Strooom/SmartTherm/docs/Blynk Interface.PNG

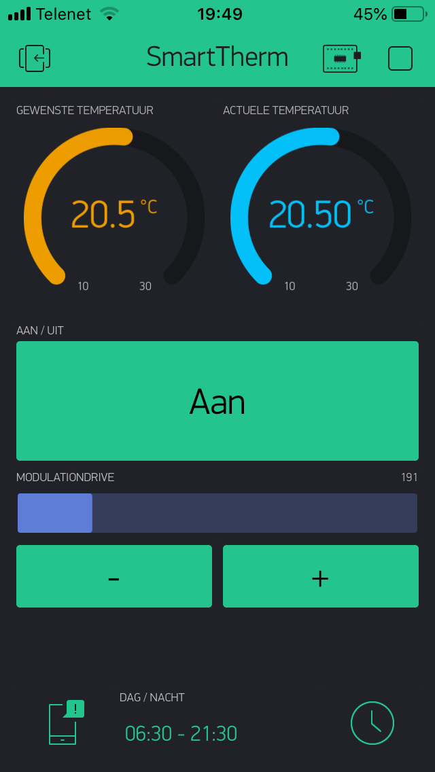
docs/Blynk Interface.PNG
