Strooom/SmartTherm/docs/microcontroller D8 output.png

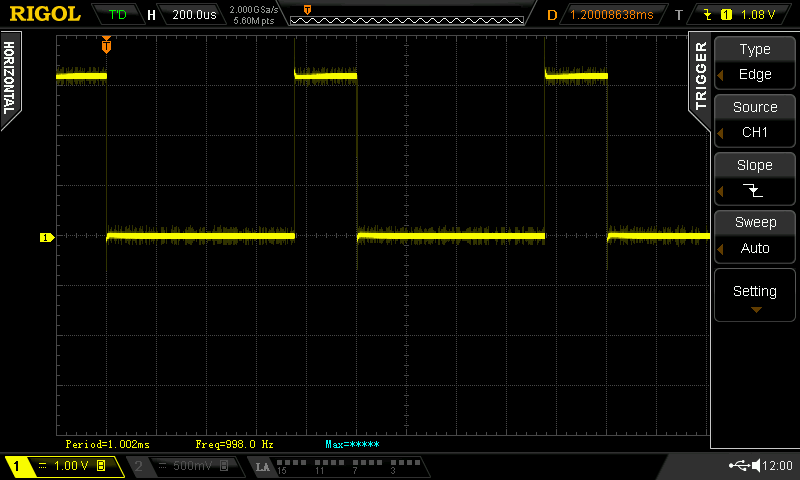
docs/microcontroller D8 output.png
