Strooom/SmartTherm/docs/opamp A output.png

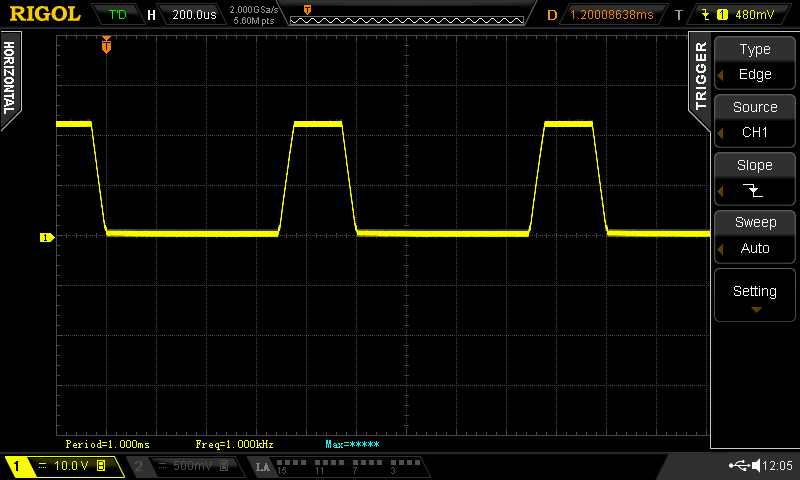
docs/opamp A output.png
