Strooom/SmartTherm/docs/opamp B output.png

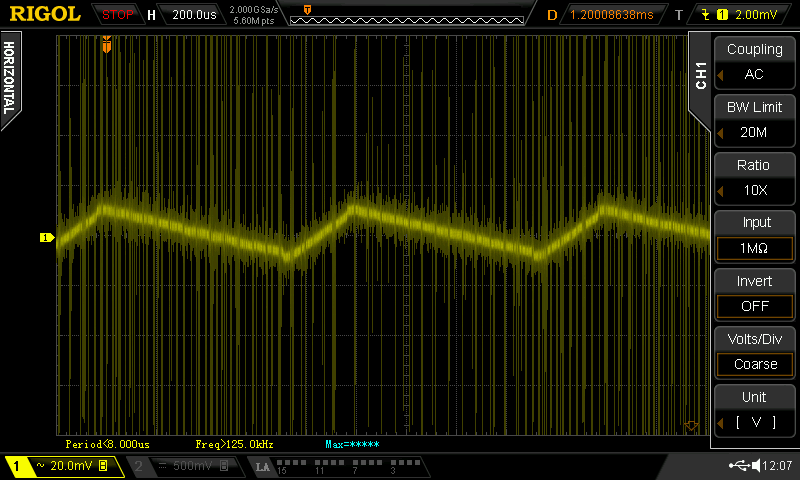
docs/opamp B output.png
