Strooom/SmartTherm/docs/optocoupler output.png

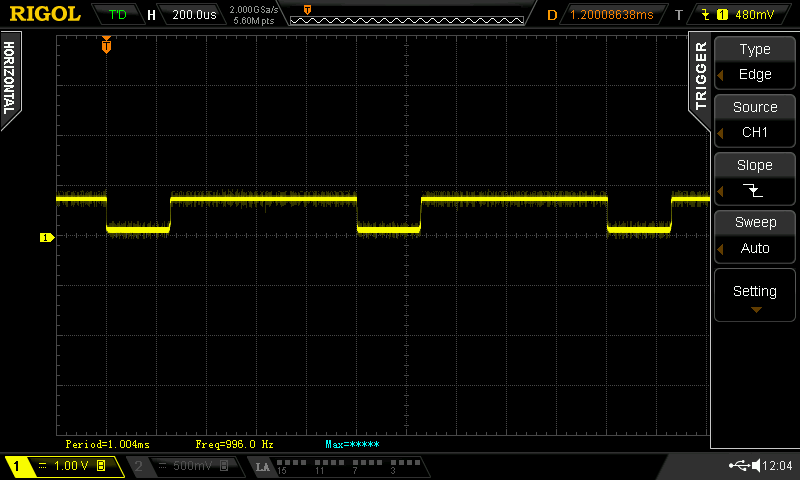
docs/optocoupler output.png
