Strooom/SmartTherm/docs/transistor output.png

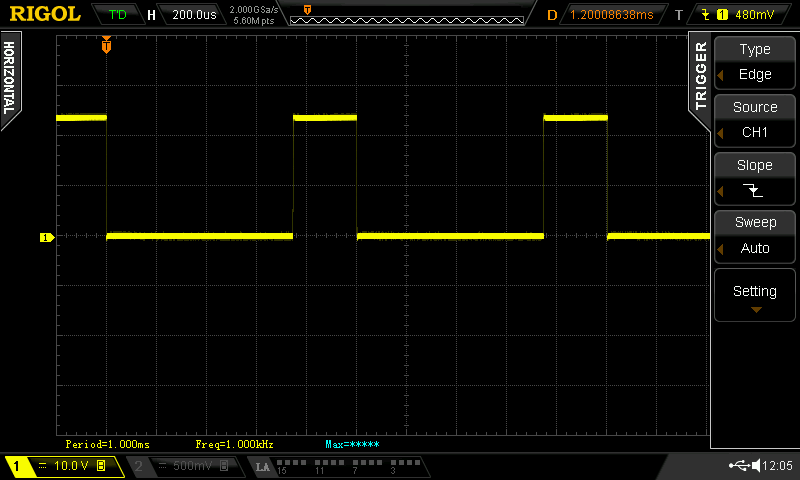
docs/transistor output.png
