Strooom/SmartTherm/outputs/pcb/openSourceProject-3D_blender_001.png

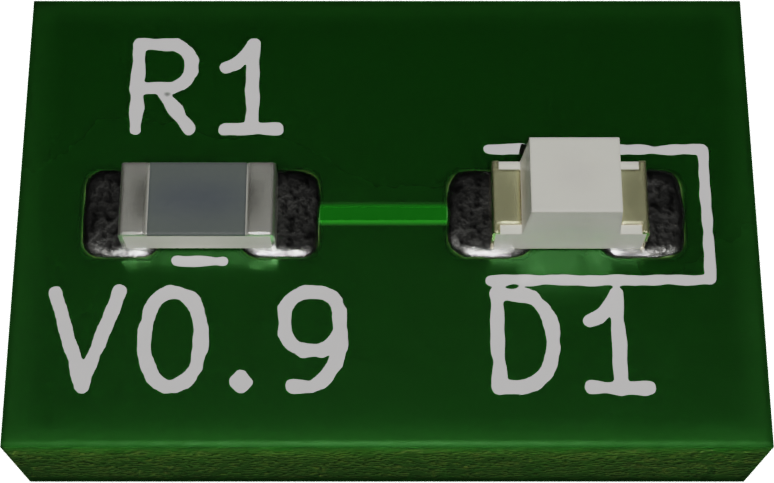
outputs/pcb/openSourceProject-3D_blender_001.png
