Strooom/SmartTherm/outputs/pcb/openSourceProject-3D_blender_002.png

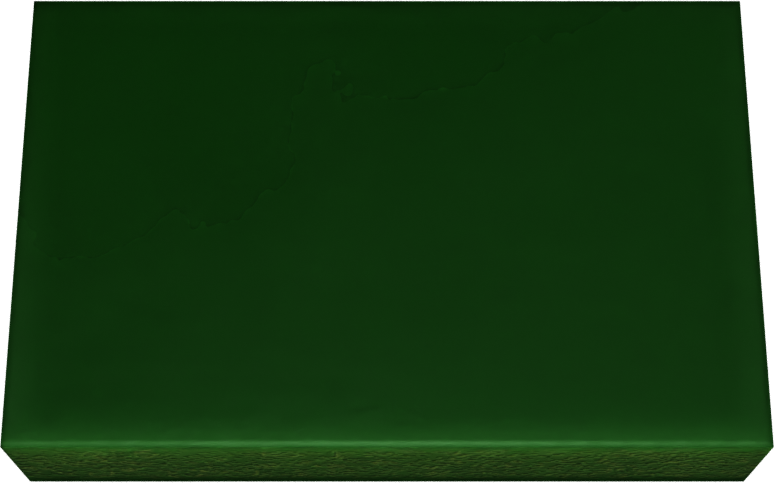
outputs/pcb/openSourceProject-3D_blender_002.png
