Strooom/SmartTherm/outputs/pcb/SmartTherm-PCB-3D_blender_001.png

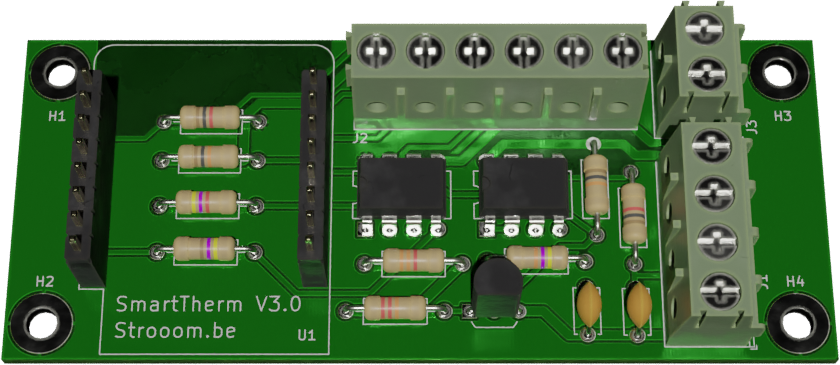
outputs/pcb/SmartTherm-PCB-3D_blender_001.png
