Strooom/SmartTherm/outputs/pcb/SmartTherm-PCB-3D_blender_002.png

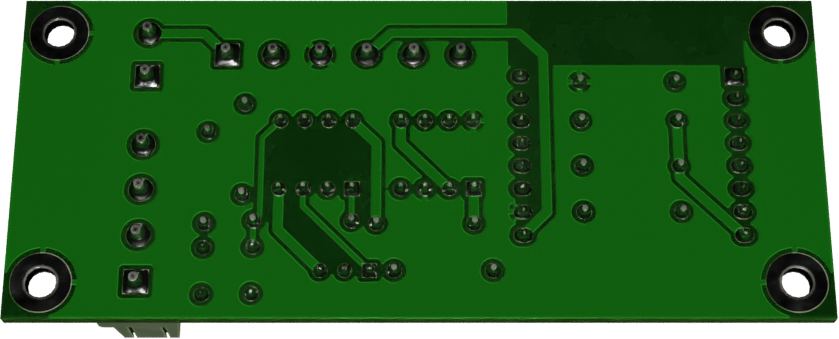
outputs/pcb/SmartTherm-PCB-3D_blender_002.png
